smitty444/IoT-Cellular-Dam-Water-Level-Sensor/figures/png files/figure_2.png

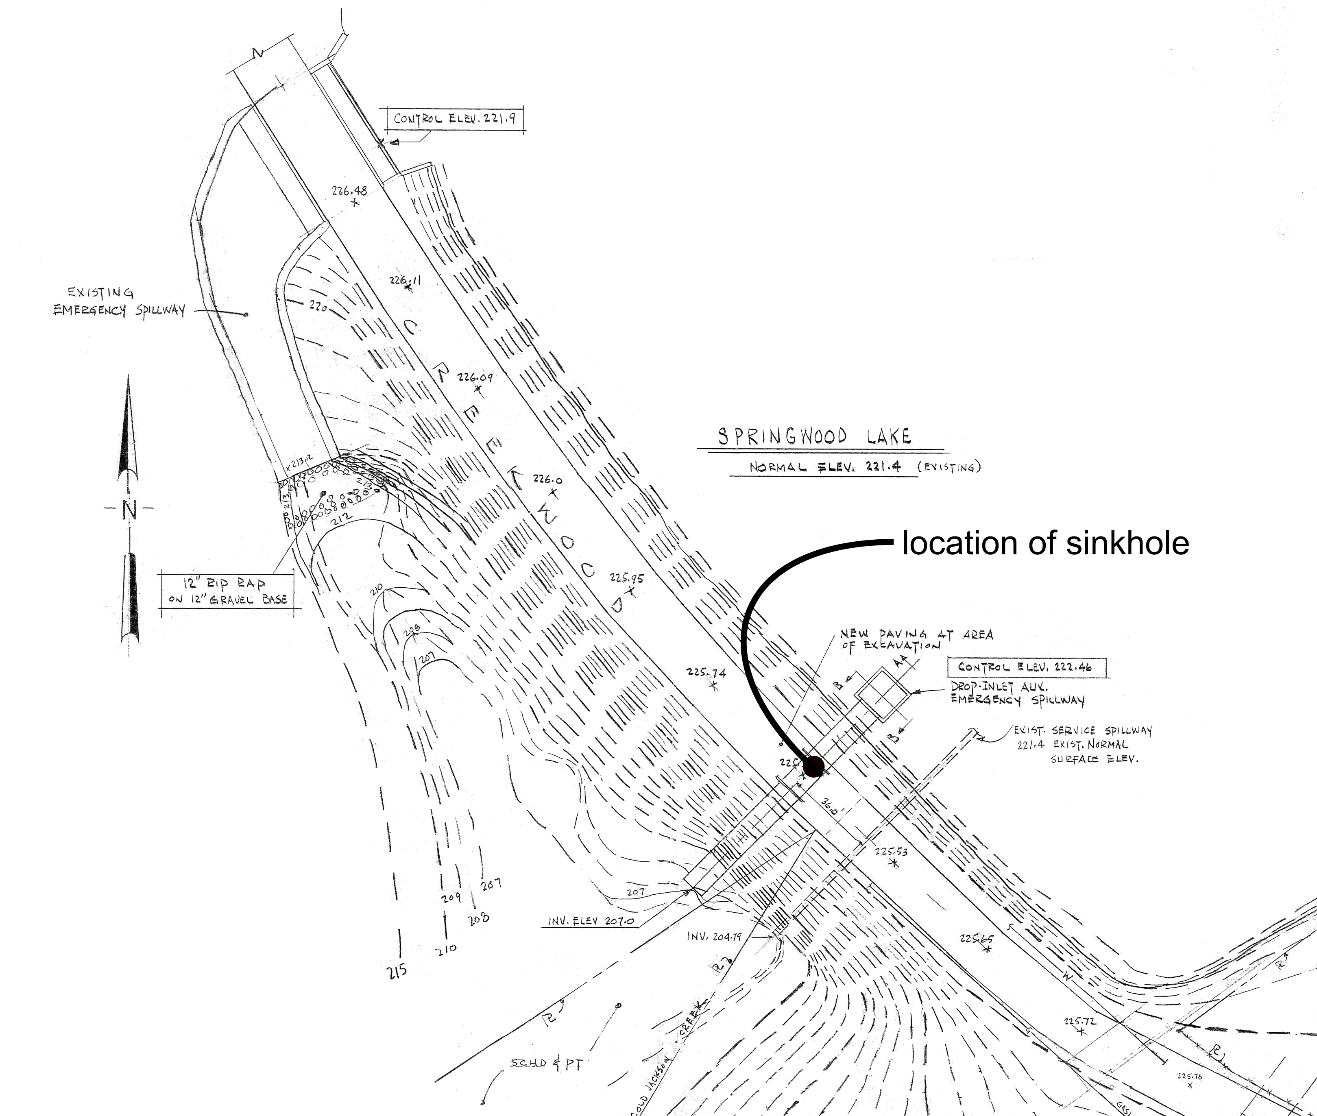
figures/png files/figure_2.png
