smitty444/IoT-Cellular-Dam-Water-Level-Sensor/figures/png files/figure_6.png

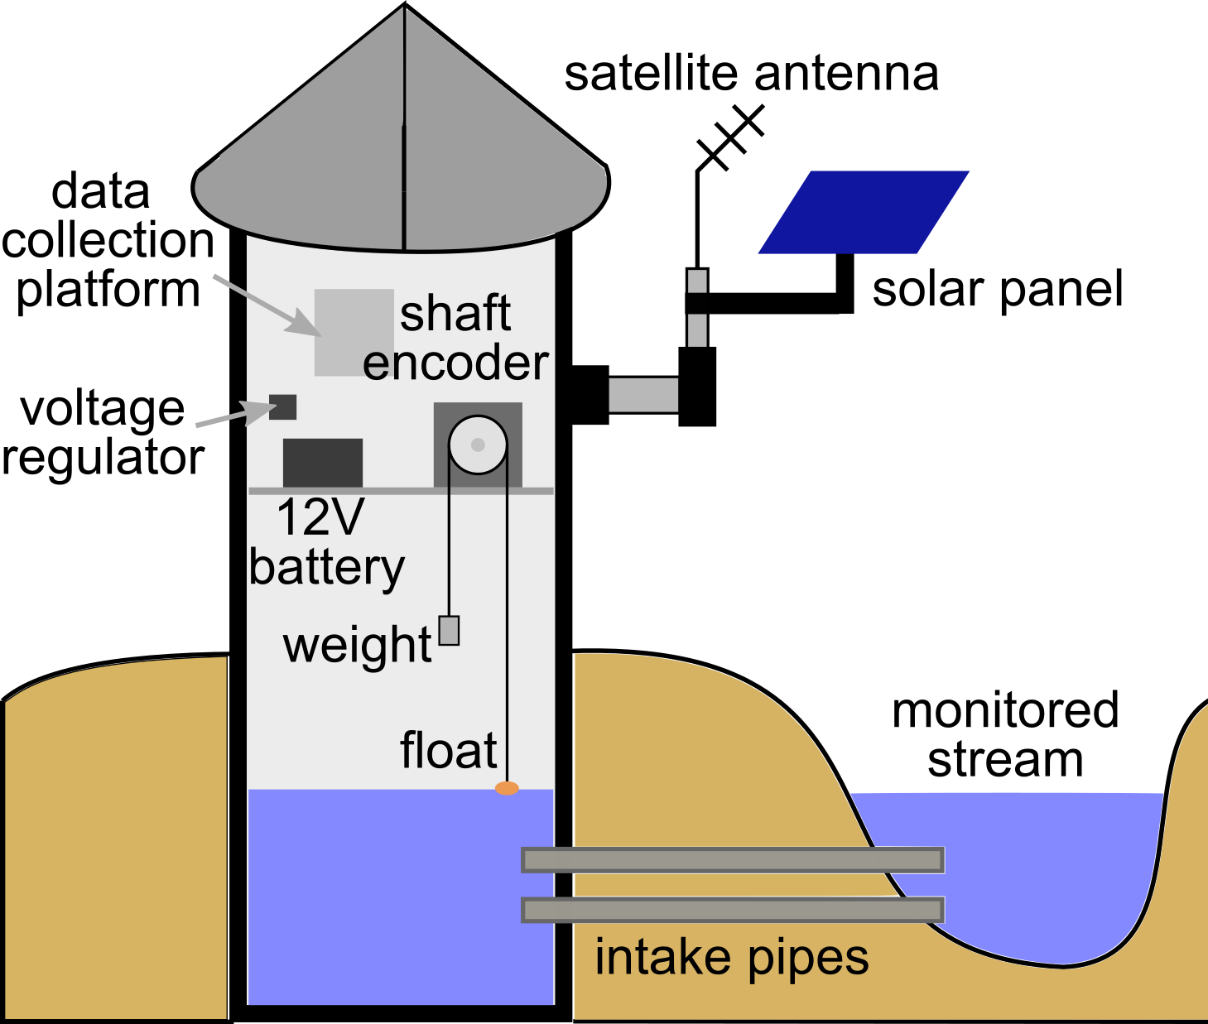
figures/png files/figure_6.png
