smitty444/IoT-Cellular-Dam-Water-Level-Sensor/figures/png files/figure_7.png

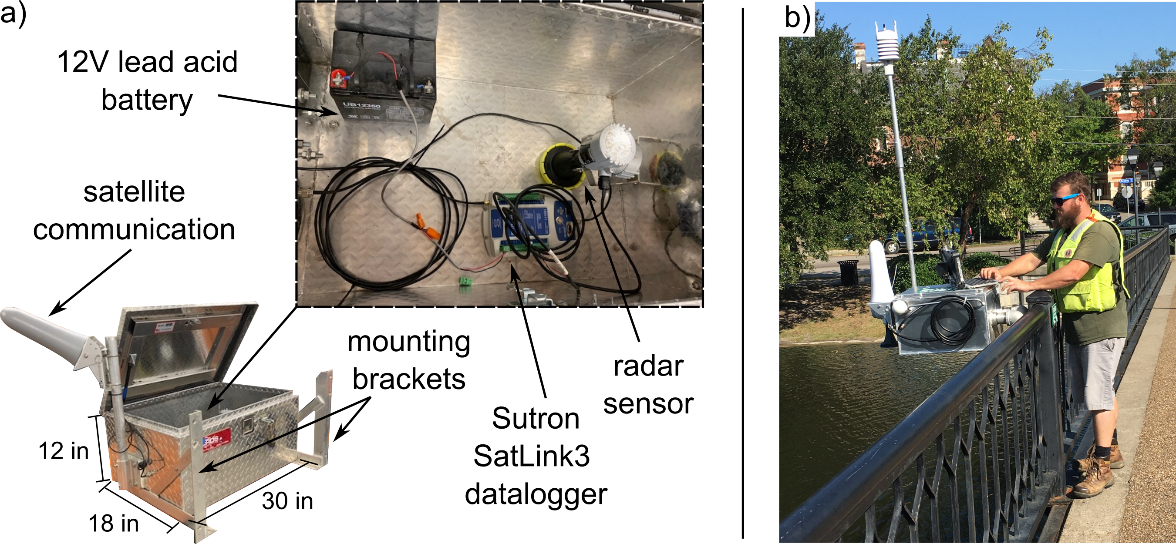
figures/png files/figure_7.png
