smitty444/IoT-Cellular-Dam-Water-Level-Sensor/figures/png files/figure_8.png

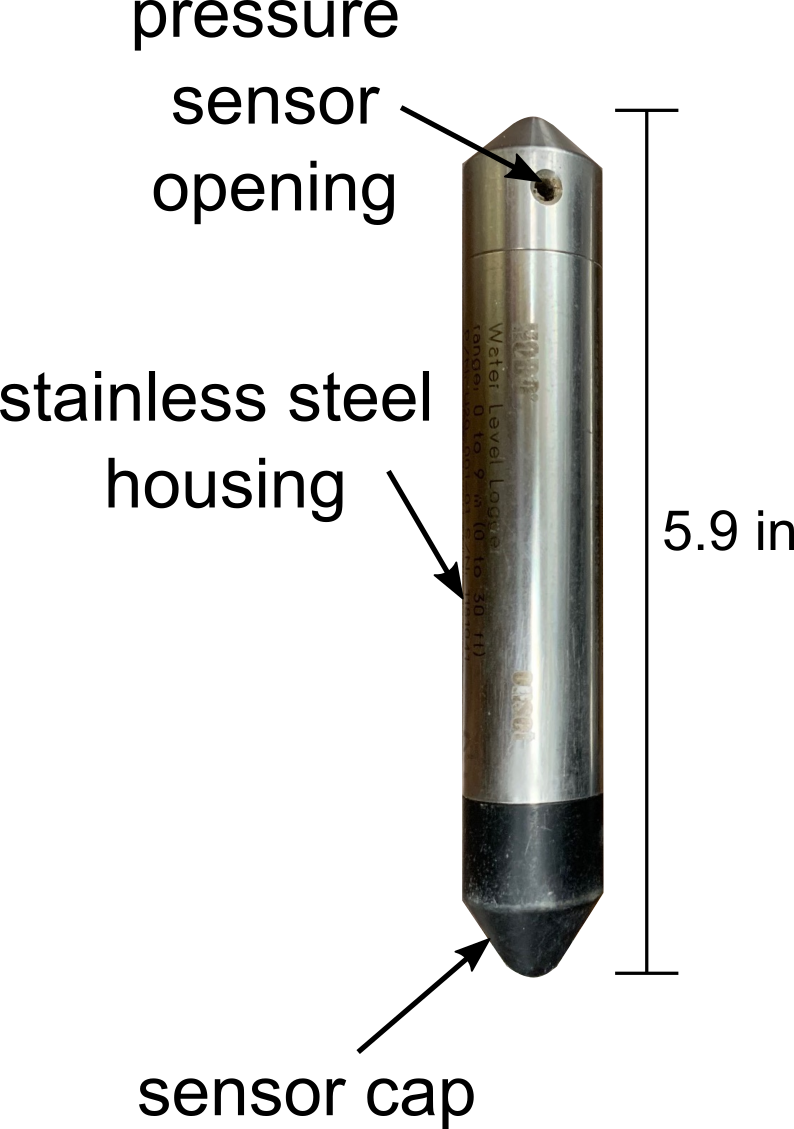
figures/png files/figure_8.png
