smitty444/IoT-Cellular-Dam-Water-Level-Sensor/figures/png files/figure_10.PNG

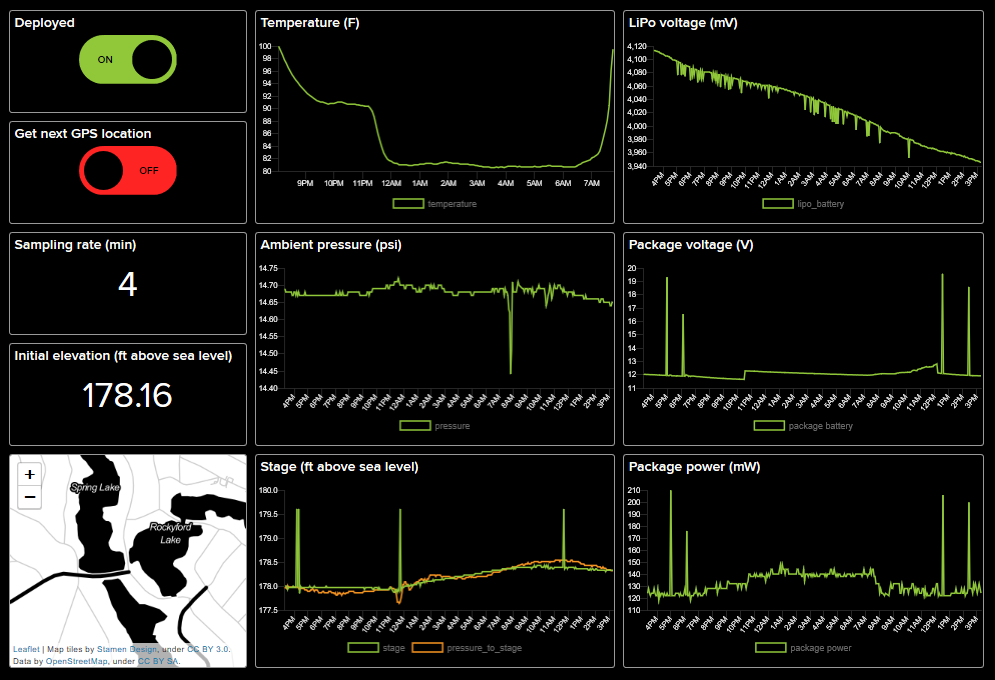
figures/png files/figure_10.PNG
