smitty444/IoT-Cellular-Dam-Water-Level-Sensor/figures/png files/figure_12.png

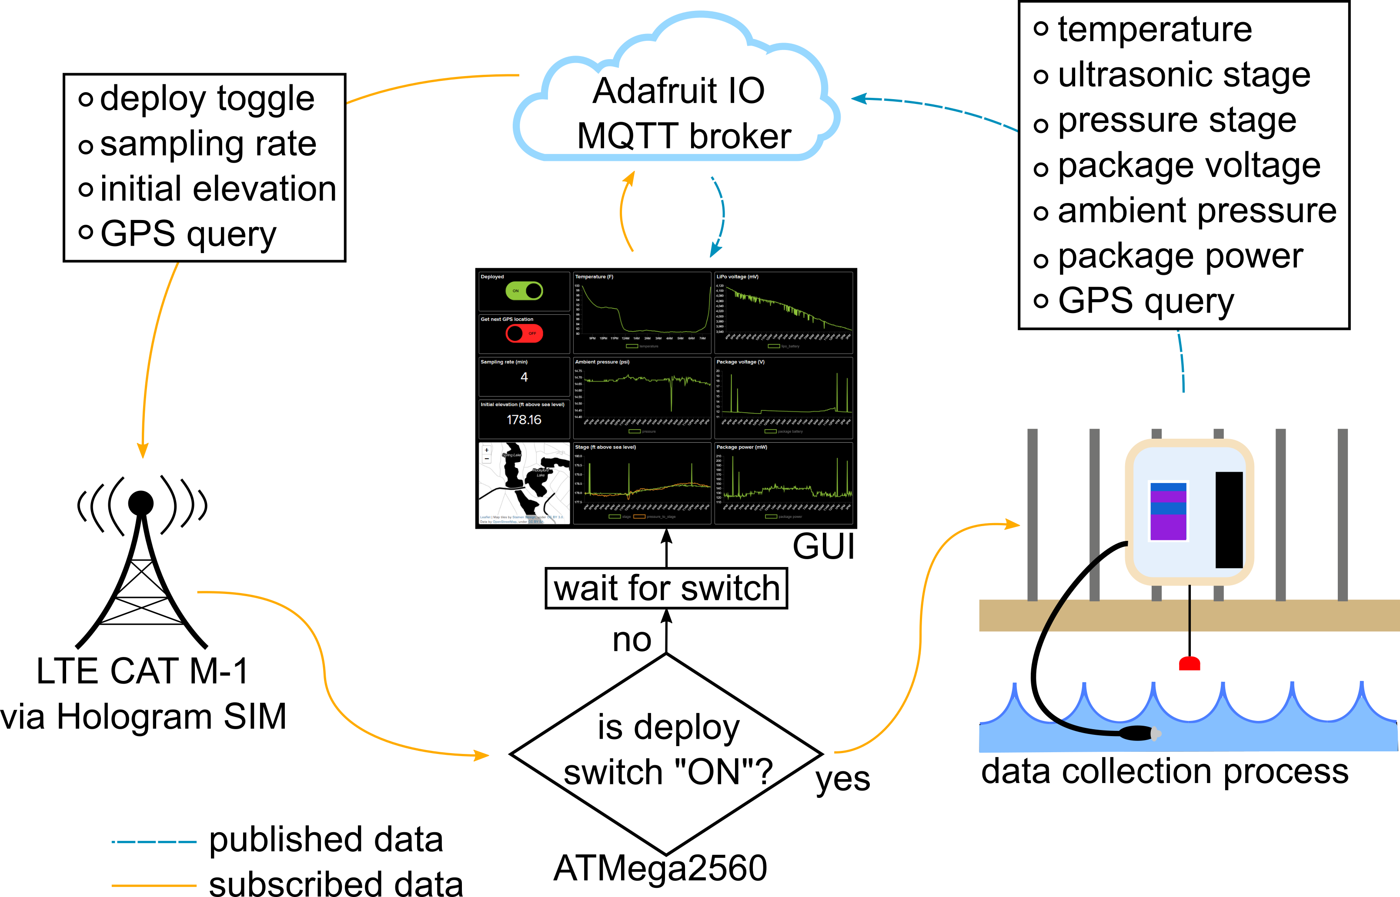
figures/png files/figure_12.png
