smitty444/IoT-Cellular-Dam-Water-Level-Sensor/field tests/03_31-04_01/adafruit_data.csv

id | value |  | date | time
0EZV0A30ZCVD64ZADP2S2CPABR | 168.17 | 1793320 | 3/31/2022 | 9:00:29 AM | 13:00:29 | UTC
0EZV0CA7WHX1M8GB4N6JHZB63J | 167.75 | 1793320 | 3/31/2022 | 9:04:22 AM | 13:04:22 | UTC
0EZV0EJTHQ139PP5T3SVMQC0PY | 168.17 | 1793320 | 3/31/2022 | 9:08:20 AM | 13:08:20 | UTC
0EZV0GVZ7S99SMK82C4YQ7F1HG | 168 | 1793320 | 3/31/2022 | 9:12:20 AM | 13:12:20 | UTC
0EZV0K57PYGC19JFYEKV123V64 | 168 | 1793320 | 3/31/2022 | 9:16:20 AM | 13:16:20 | UTC
0EZV0NEFFPF2SAD7G998VVKM82 | 168.25 | 1793320 | 3/31/2022 | 9:20:20 AM | 13:20:20 | UTC
0EZV0QQV3GREM1TBYWMZNEH33Q | 168 | 1793320 | 3/31/2022 | 9:24:20 AM | 13:24:20 | UTC
0EZV0T11BVVX4H63BTK15TCRVP | 168 | 1793320 | 3/31/2022 | 9:28:20 AM | 13:28:20 | UTC
0EZV0WAAKZHXYNG5JFSJ0W4KAG | 168.17 | 1793320 | 3/31/2022 | 9:32:20 AM | 13:32:20 | UTC
0EZV0YKG0JDS6T2SAYEWVF0FKJ | 168 | 1793320 | 3/31/2022 | 9:36:20 AM | 13:36:20 | UTC
0EZV10WQQY0AFNJNZRD3AAT95Z | 168 | 1793320 | 3/31/2022 | 9:40:20 AM | 13:40:20 | UTC
0EZV13614WY62KXTCX5F2C9132 | 168 | 1793320 | 3/31/2022 | 9:44:20 AM | 13:44:20 | UTC
0EZV15F8T352SQ2JM1VTGAD7DA | 168.17 | 1793320 | 3/31/2022 | 9:48:20 AM | 13:48:20 | UTC
0EZV17RFT97XHA0Q4V5PTZWCE1 | 167.75 | 1793320 | 3/31/2022 | 9:52:20 AM | 13:52:20 | UTC
0EZV1A2HBNY57RMDK78269FQFN | 168 | 1793320 | 3/31/2022 | 9:56:23 AM | 13:56:23 | UTC
0EZV1CAW69E2YGNFWJRMJ530AD | 168.17 | 1793320 | 3/31/2022 | 10:00:20 AM | 14:00:20 | UTC
0EZV1EM68726FVT20AXN0JYE08 | 168 | 1793320 | 3/31/2022 | 10:04:20 AM | 14:04:20 | UTC
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
0EZV9R4A2T86YZZDMTKJ365V33 | 168.17 | 1793320 | 3/31/2022 | 5:48:20 PM | 21:48:20 | UTC
0EZV9TDHZNWE0NC81VS7DMAD9N | 166.58 | 1793320 | 3/31/2022 | 5:52:20 PM | 21:52:20 | UTC
0EZV9WPRSB7JZJH57WCVE74HJQ | 168.17 | 1793320 | 3/31/2022 | 5:56:20 PM | 21:56:20 | UTC
0EZV9YZZSN6W7RRVJH97BW5DBZ | 168.25 | 1793320 | 3/31/2022 | 6:00:20 PM | 22:00:20 | UTC
0EZVA197KNPE57057DX6A4W8BD | 167.92 | 1793320 | 3/31/2022 | 6:04:20 PM | 22:04:20 | UTC
0EZVA3JGWBS59XX5QYX4TV8R3H | 168.08 | 1793320 | 3/31/2022 | 6:08:20 PM | 22:08:20 | UTC
0EZVA5VRHB75HB5RRC1F5R4J8V | 168.08 | 1793320 | 3/31/2022 | 6:12:20 PM | 22:12:20 | UTC
0EZVA850CHY377BN578CY1AJ42 | 168.08 | 1793320 | 3/31/2022 | 6:16:20 PM | 22:16:20 | UTC
0EZVAAE84DKARCQDCARDAVFDRP | 168.17 | 1793320 | 3/31/2022 | 6:20:20 PM | 22:20:20 | UTC
0EZVACQFTMKKH03ERDSVD2PCPG | 168.08 | 1793320 | 3/31/2022 | 6:24:20 PM | 22:24:20 | UTC
0EZVAF0N915FQ3Y25JC1AJ4SNX | 168.17 | 1793320 | 3/31/2022 | 6:28:20 PM | 22:28:20 | UTC
0EZVAHAPR5B9YWAW657YVWJ0AJ | 170.5 | 1793320 | 3/31/2022 | 6:32:22 PM | 22:32:22 | UTC
