smitty444/IoT-Cellular-Dam-Water-Level-Sensor/field tests/04_06-04_07/adaptive_stage_data.csv

id | value | feed_id | date | time |  |  | ele
0F000A2E683CP9Z2FPAW33Q6XY | 168 | 1852686 | 4/6/2022 | 2:08:18 PM | 18:08:18 | UTC
0F000CJ5GHQDTNZ8M9BKKKCZ3N | 168 | 1852686 | 4/6/2022 | 2:12:39 PM | 18:12:39 | UTC
0F000EN4NGKDEB6C7WZNG3KRSN | 168 | 1852686 | 4/6/2022 | 2:16:18 PM | 18:16:18 | UTC
0F000H62DNR232TS594GWHQDNB | 167.92 | 1852686 | 4/6/2022 | 2:20:44 PM | 18:20:44 | UTC
0F000K7M1ERVVZAXXHQNMTTKFP | 168.08 | 1852686 | 4/6/2022 | 2:24:18 PM | 18:24:18 | UTC
0F000NRE4KKKMK58SK372A60WY | 168 | 1852686 | 4/6/2022 | 2:28:43 PM | 18:28:43 | UTC
0F000R1SQGY2RP2P2S5NM11JAK | 168.08 | 1852686 | 4/6/2022 | 2:32:44 PM | 18:32:44 | UTC
0F000TKE6YKZ083F0WXGNE38G1 | 168 | 1852686 | 4/6/2022 | 2:37:11 PM | 18:37:11 | UTC
0F000TNFPW849TB69AZT9A5CZ9 | 168.08 | 1852686 | 4/6/2022 | 2:37:18 PM | 18:37:18 | UTC
0F000YNT4MXYXWMTSGYKRA9N2Y | 168 | 1852686 | 4/6/2022 | 2:44:18 PM | 18:44:18 | UTC
0F0013D4WYWQ941PDKEF0AF2ED | 169.75 | 1852686 | 4/6/2022 | 2:52:34 PM | 18:52:34 | UTC
0F0015Q8ZHQ8P5JZGJE6ZND8DT | 168 | 1852686 | 4/6/2022 | 2:56:37 PM | 18:56:37 | UTC
0F00181MTYJX59KT728JTHKZPJ | 168 | 1852686 | 4/6/2022 | 3:00:41 PM | 19:00:41 | UTC
0F001AB11ZWP02SF6DMZSCY8SF | 167.92 | 1852686 | 4/6/2022 | 3:04:41 PM | 19:04:41 | UTC
0F001CVWRAY5W0FTNFHCXNFRBQ | 167.83 | 1852686 | 4/6/2022 | 3:09:06 PM | 19:09:06 | UTC
0F001CXY63ZSJ8GJQHMQBKYKWW | 168 | 1852686 | 4/6/2022 | 3:09:13 PM | 19:09:13 | UTC
0F001FEWXTN441B0CQ2ZGCJP35 | 168.08 | 1852686 | 4/6/2022 | 3:13:38 PM | 19:13:38 | UTC
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
0F007VHHYGFH24MYF0ND3GMD08 | 168.58 | 1852686 | 4/6/2022 | 9:10:18 PM | 1:10:18 | UTC
0F007XTSQB3P59D7B53ZAPN3XQ | 168.58 | 1852686 | 4/6/2022 | 9:14:18 PM | 1:14:18 | UTC
0F008042XX5VETC2B132SS4ZVF | 168.58 | 1852686 | 4/6/2022 | 9:18:18 PM | 1:18:18 | UTC
