smitty444/IoT-Cellular-Dam-Water-Level-Sensor/characteristic data/Pressure Sensor Calibration AIO Data/hobo_test_june14/DHEC_HOBO_DATA.xlsx

Sheet: Processed data
# | Date Time, GMT-04:00 | Abs Pres, psi (LGR S/N: 1181041, SEN S/N: 1181041) | Temp, °F (LGR S/N: 1181041, SEN S/N: 1181041) | Abs Pres Barom., psi (LGR S/N: 1181036, SEN S/N: 1181036) | Sensor Depth, feet (LGR S/N: 1181041) | Pressure differential
405 | 2022-06-14 13:00 | 14.6318 | 72.545 | 14.6314 | 0.001 | 0.0004
406 | 2022-06-14 13:15 | 15.1897 | 77.4 | 14.6258 | 1.301 | 0.5639
407 | 2022-06-14 13:30 | 15.1872 | 77.4 | 14.6247 | 1.297 | 0.5625
408 | 2022-06-14 13:45 | 15.1984 | 77.225 | 14.6382 | 1.292 | 0.5602
409 | 2022-06-14 14:00 | 15.2024 | 77.05 | 14.6426 | 1.291 | 0.5598
410 | 2022-06-14 14:15 | 15.2024 | 77.05 | 14.6395 | 1.298 | 0.5629
411 | 2022-06-14 14:30 | 15.2011 | 76.703 | 14.6392 | 1.296 | 0.5619
412 | 2022-06-14 14:45 | 15.2017 | 73.58 | 14.6391 | 1.298 | 0.5626
413 | 2022-06-14 15:00 | 15.2037 | 71.512 | 14.6411 | 1.298 | 0.5626
414 | 2022-06-14 15:15 | 15.1972 | 70.995 | 14.6391 | 1.287 | 0.5581
415 | 2022-06-14 15:30 | 15.1978 | 70.48 | 14.6417 | 1.283 | 0.5561
416 | 2022-06-14 15:45 | 15.1918 | 70.137 | 14.6375 | 1.279 | 0.5543
417 | 2022-06-14 16:00 | 15.1865 | 69.964 | 14.6333 | 1.276 | 0.5532
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
