smitty444/IoT-Cellular-Dam-Water-Level-Sensor/field tests/05_12-05_17/pressure_data.csv

stage | ambient |  |  |  | ambient (ft) | error |  | ultrasonic |  | corrected pts | raw pressure
150.01 | 14.7 | 1794775 | 5/12/2022 | 21:05:15 | 0 | 0.01 | 1 | 150 | 150.01 | 150.01 | 150.01
150.01 | 14.7 | 1794775 | 5/12/2022 | 21:08:45 | 0 | 0.09 | 2 | 149.92 | 150.01 | 150.01 | 150.01
150.01 | 14.7 | 1794775 | 5/12/2022 | 21:12:45 | 0 | 0.09 | 3 | 149.92 | 150.01 | 150.01 | 150.01
150.01 | 14.7 | 1794775 | 5/12/2022 | 21:16:45 | 0 | 0.09 | 4 | 149.92 | 150.01 | 150.01 | 150.01
150.01 | 14.7 | 1794775 | 5/12/2022 | 21:20:45 | 0 | 0.09 | 5 | 149.92 | 150.01 | 150.01 | 150.01
150.01 | 14.7 | 1794775 | 5/12/2022 | 21:24:45 | 0 | 0.09 | 6 | 149.92 | 150.01 | 150.01 | 150.01
150.01 | 14.71 | 1794775 | 5/12/2022 | 21:28:45 | 0.023072494 | 0.09 | 7 | 149.92 | 150.0330725 | 149.9869275 | 150.01
150.03 | 14.71 | 1794775 | 5/12/2022 | 21:32:45 | 0.023072494 | 0.11 | 8 | 149.92 | 150.0530725 | 150.0069275 | 150.03
150.06 | 14.71 | 1794775 | 5/12/2022 | 21:36:45 | 0.023072494 | 0.06 | 9 | 150 | 150.0830725 | 150.0369275 | 150.06
150.09 | 14.71 | 1794775 | 5/12/2022 | 21:40:45 | 0.023072494 | 0.09 | 10 | 150 | 150.1130725 | 150.0669275 | 150.09
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
