smitty444/IoT-Cellular-Dam-Water-Level-Sensor/characteristic data/adaptive_simulations/reverse_sigmoid.png

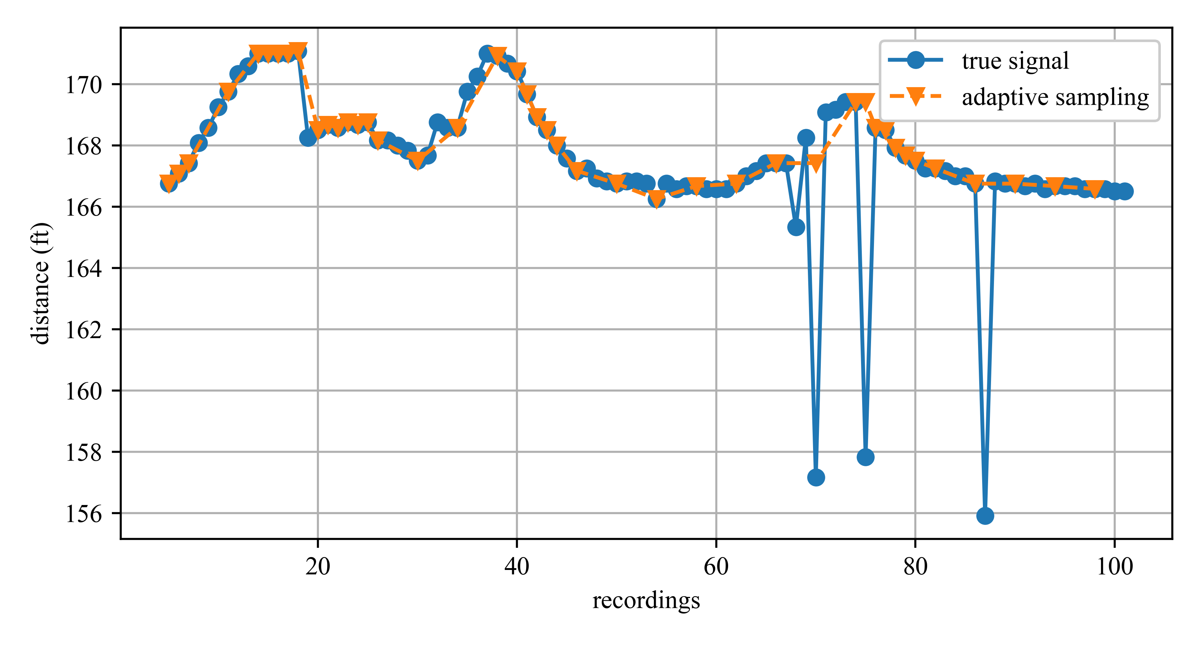
characteristic data/adaptive_simulations/reverse_sigmoid.png
