smitty444/IoT-Cellular-Dam-Water-Level-Sensor/characteristic data/filtering/arduino_plots/median_filter.png

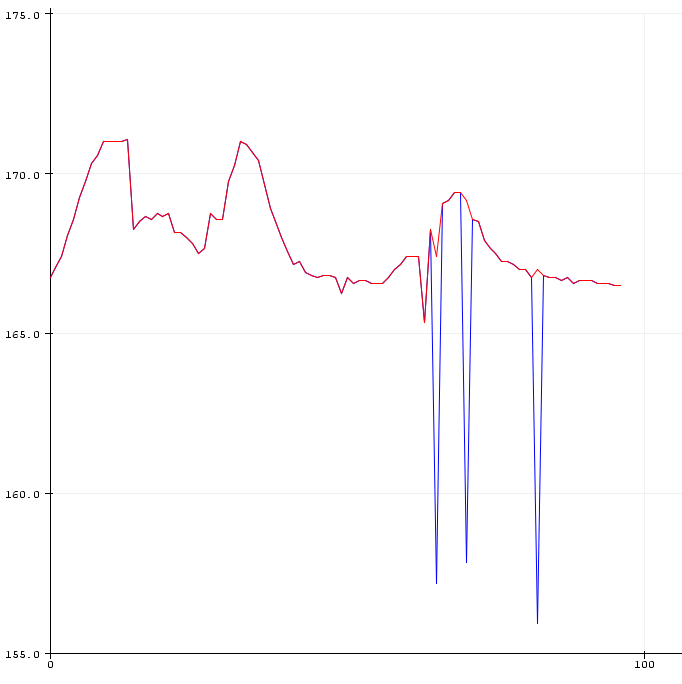
characteristic data/filtering/arduino_plots/median_filter.png
