smitty444/IoT-Cellular-Dam-Water-Level-Sensor/characteristic data/filtering/filters.png

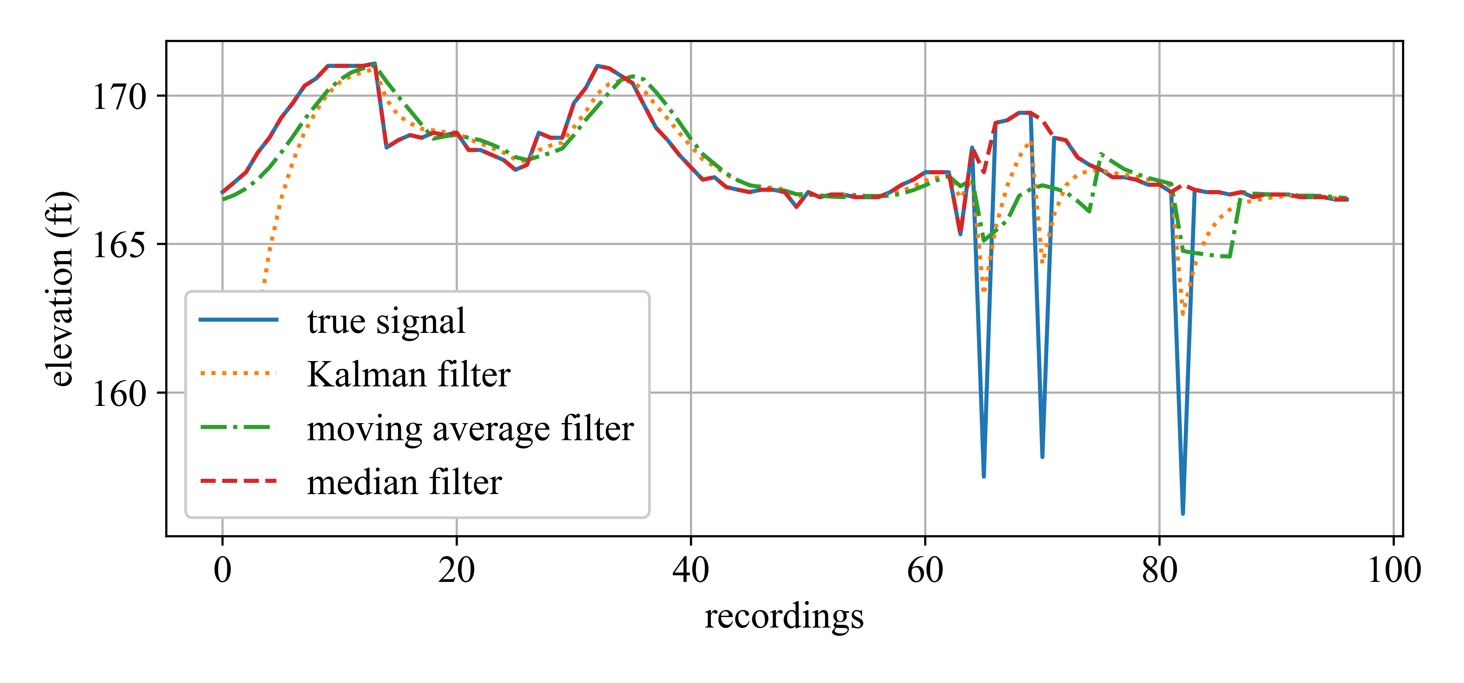
characteristic data/filtering/filters.png
