smitty444/IoT-Cellular-Dam-Water-Level-Sensor/field tests/05_03-05_09/adaptive.png

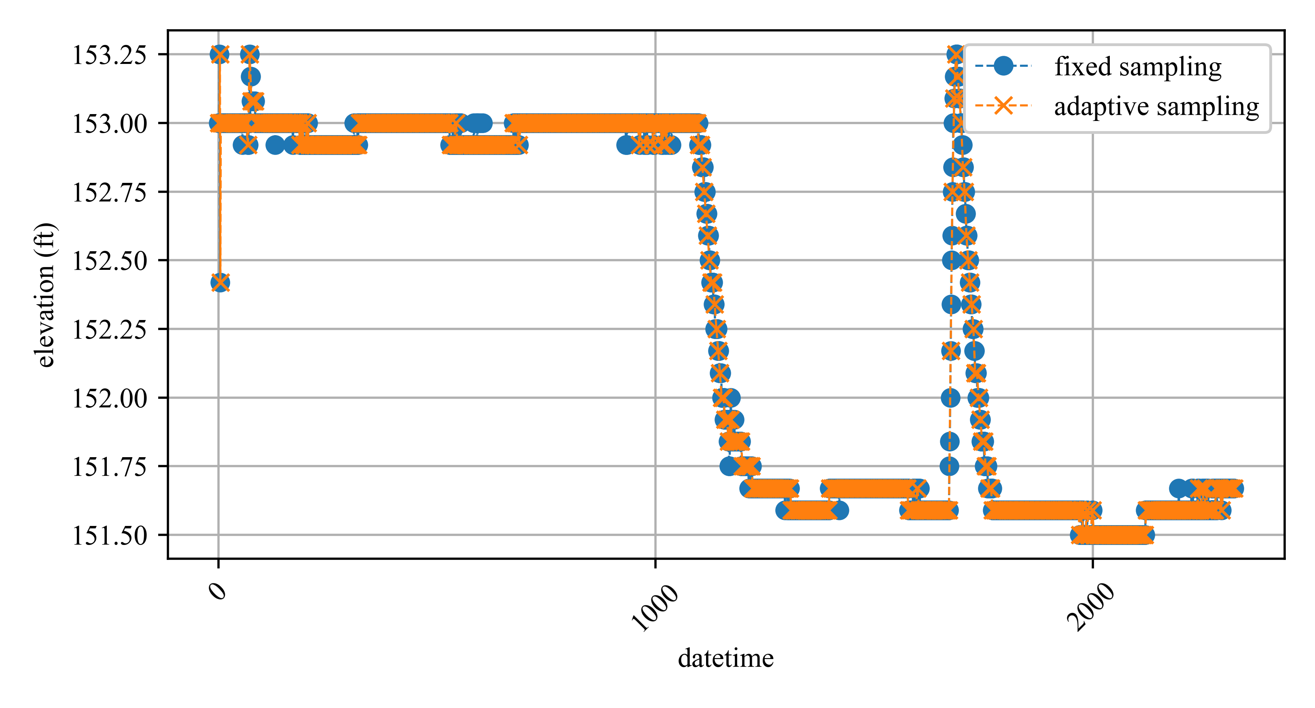
field tests/05_03-05_09/adaptive.png
