smitty444/IoT-Cellular-Dam-Water-Level-Sensor/field tests/06_14-06_27/data_filtered.png

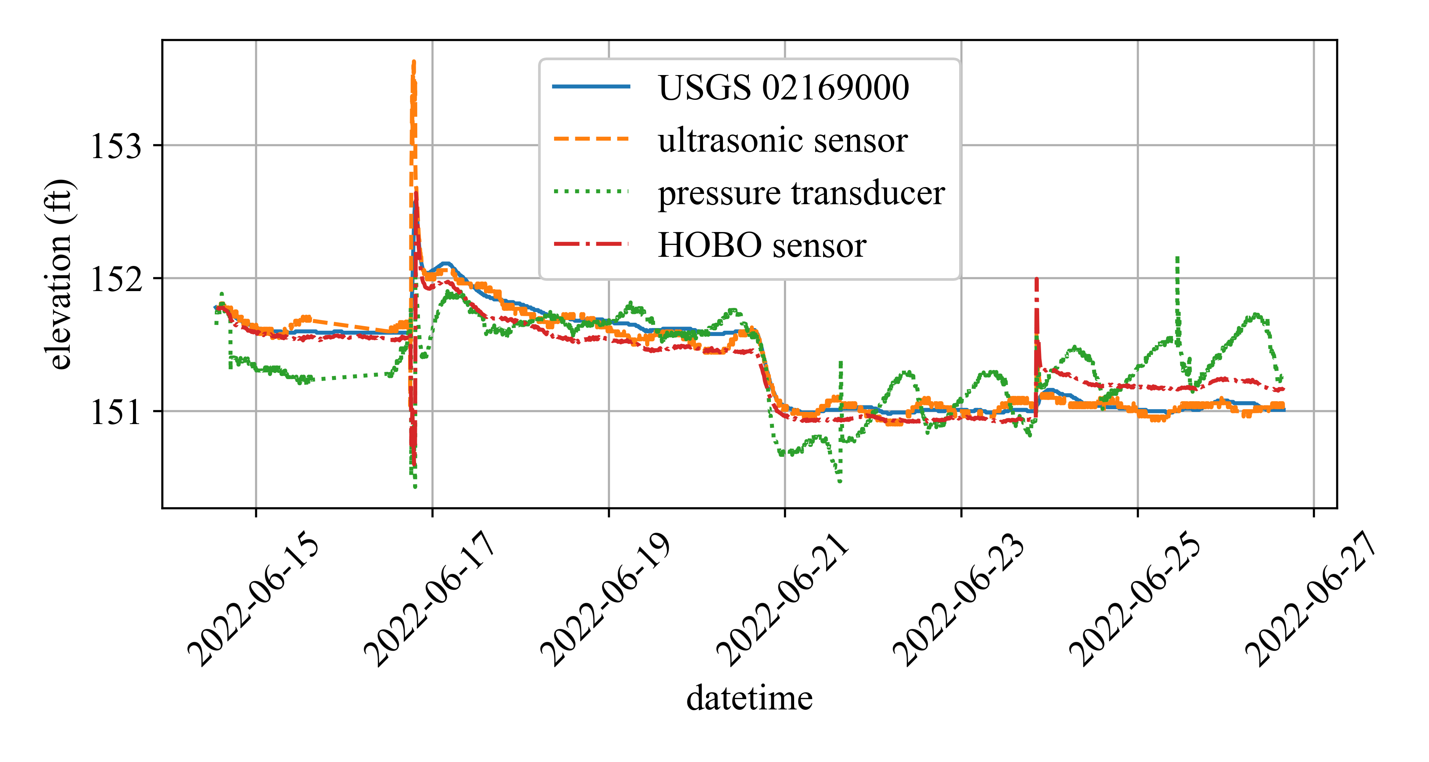
field tests/06_14-06_27/data_filtered.png
