smitty444/IoT-Cellular-Dam-Water-Level-Sensor/field tests/07_01-07_15/rainfall.png

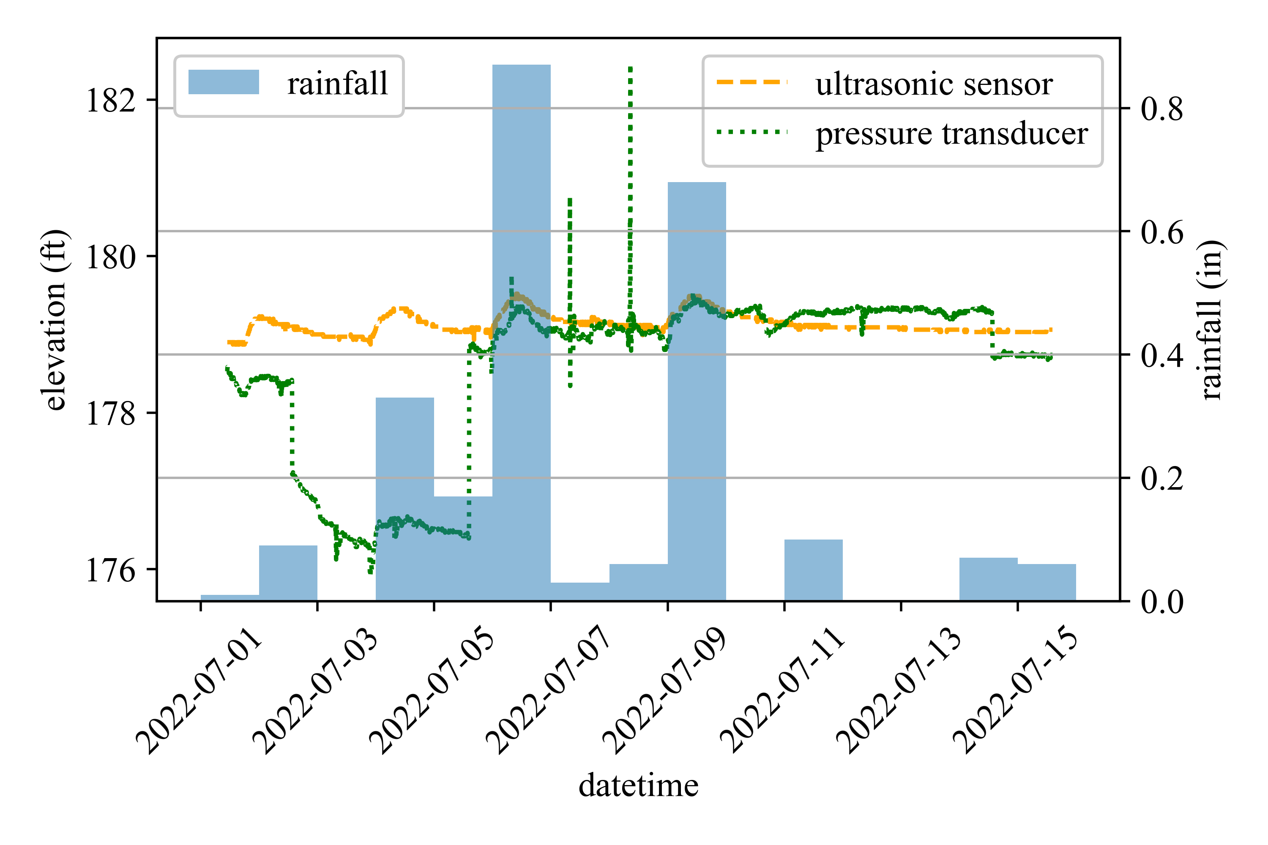
field tests/07_01-07_15/rainfall.png
