smitty444/IoT-Cellular-Dam-Water-Level-Sensor/code/debugging/plotting/kalman_filter.PNG

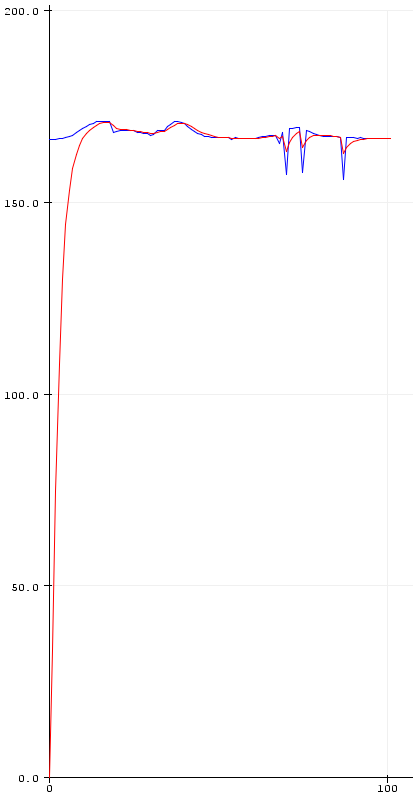
code/debugging/plotting/kalman_filter.PNG
